wuxx/TD4-4BIT-CPU/doc/TD4-black-2.jpg

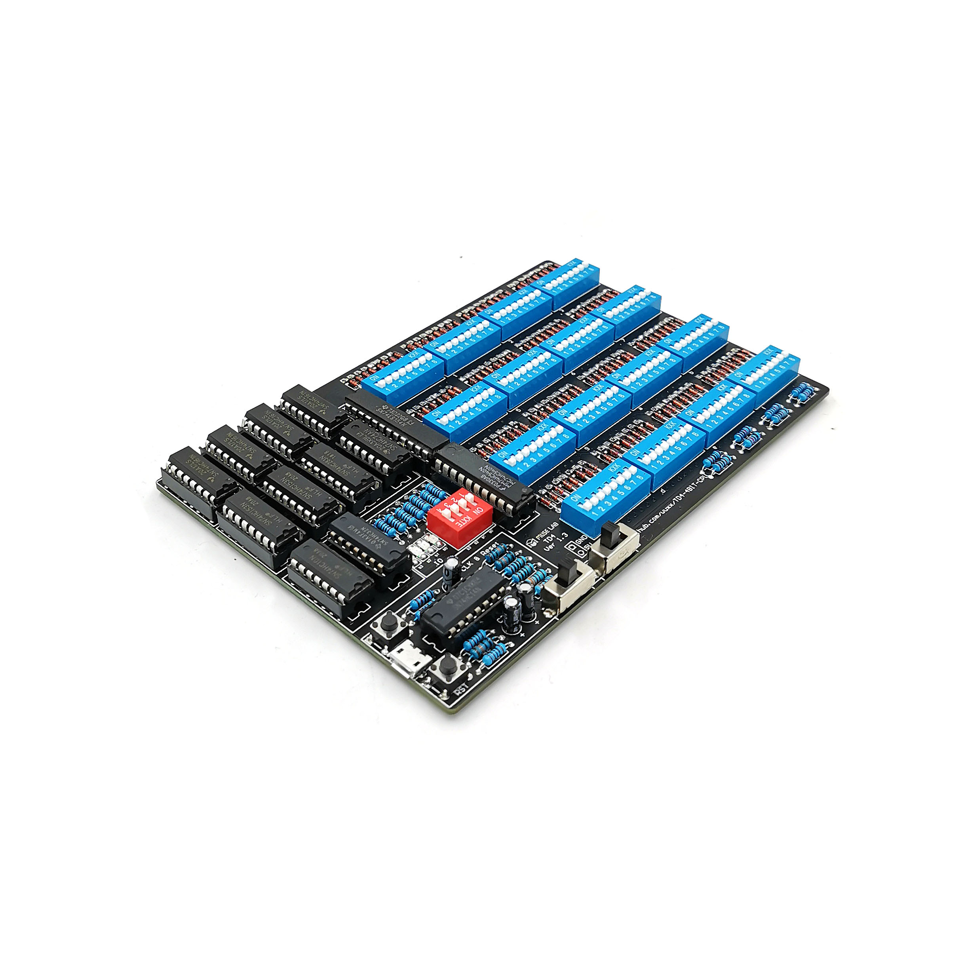
doc/TD4-black-2.jpg
