wuxx/TD4-4BIT-CPU/software/test/screenshot.png

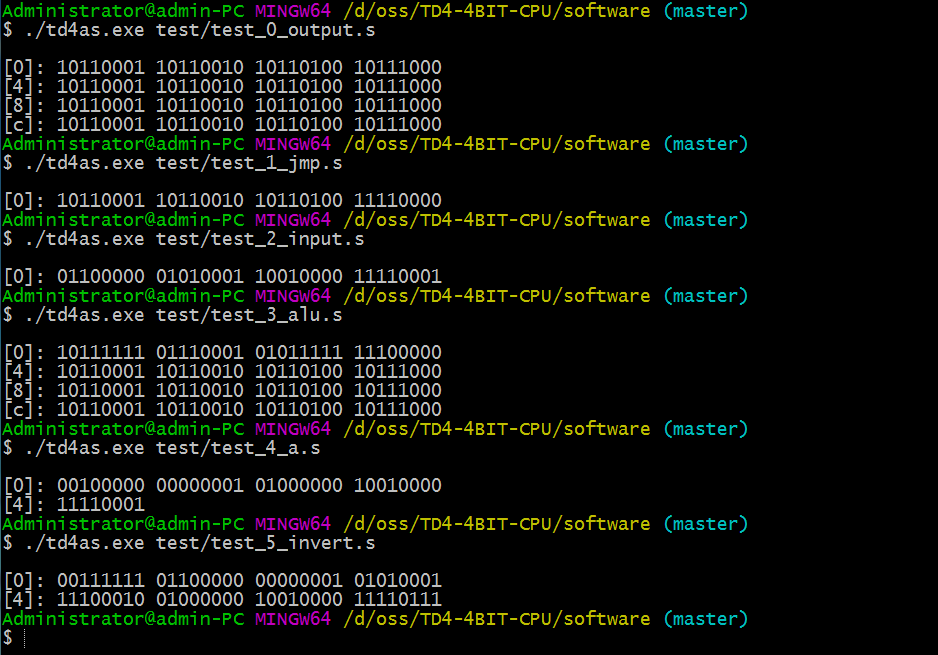
software/test/screenshot.png
